ibovegar/nobs-fs-panel/images/nobs_panel_front.png

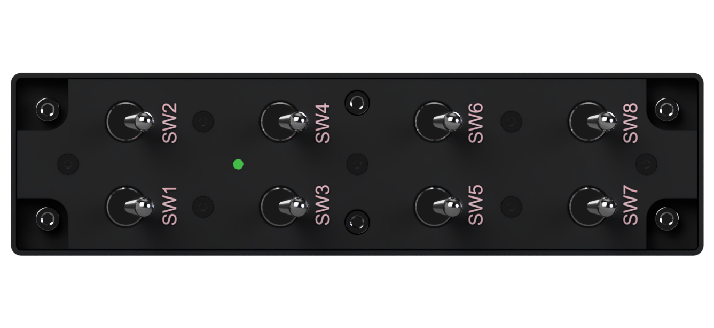
images/nobs_panel_front.png
