ibovegar/nobs-fs-panel/images/nobs_panel_front_1.png

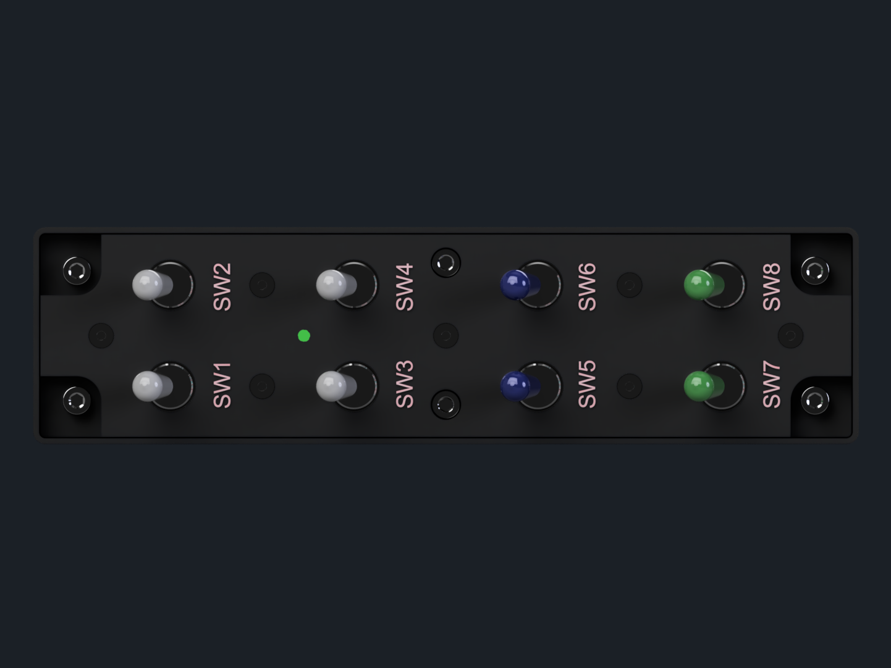
images/nobs_panel_front_1.png
