ibovegar/nobs-fs-panel/images/nobs_panel_front_2.png

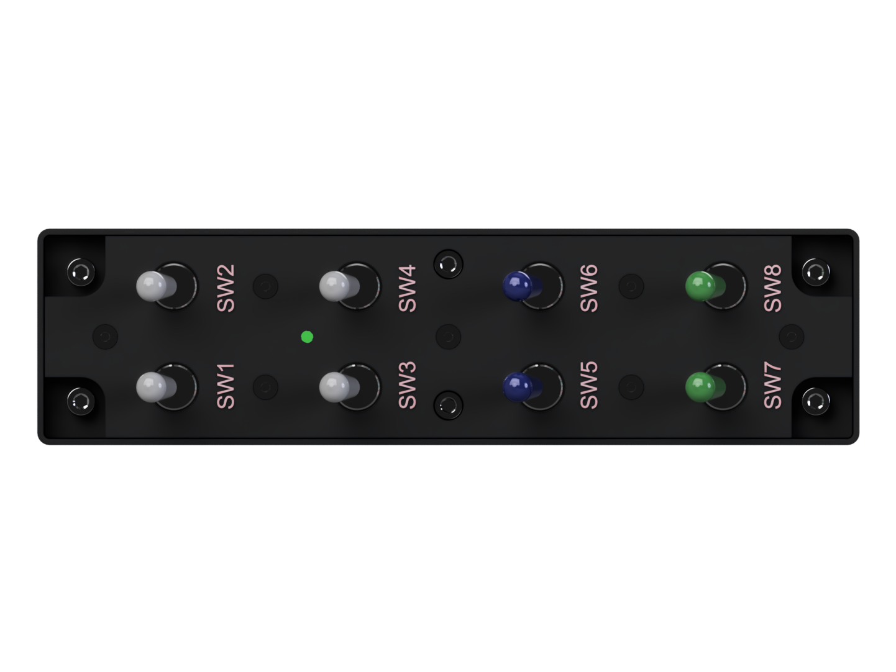
images/nobs_panel_front_2.png
